ytani01/NixieClock/docs/clock2.jpg

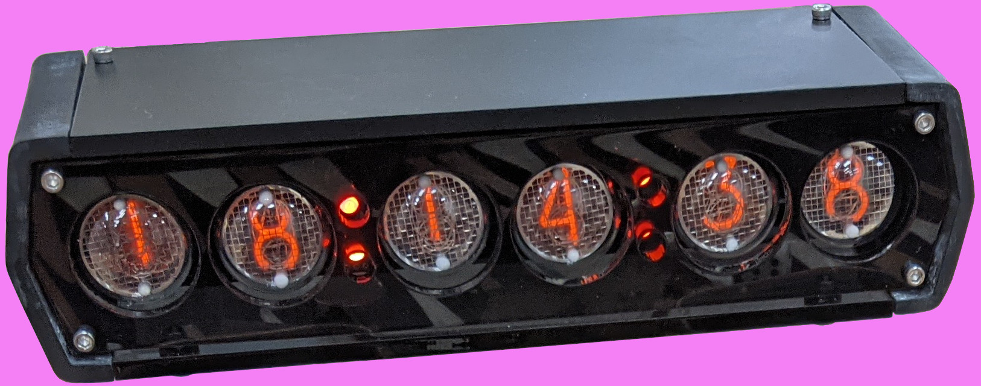
docs/clock2.jpg
