ytani01/NixieClock/Stand/Stand3/Stand3.png

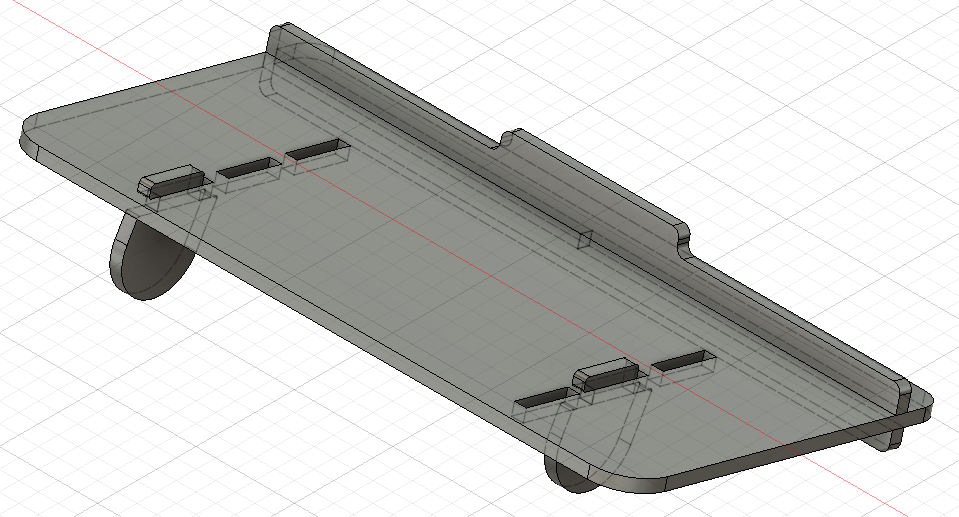
Stand/Stand3/Stand3.png
