ytani01/NixieClock/IN-16/fromTakao/IN-16_Nixie_Clock/drawing/Top_Drawing_0827.dxf

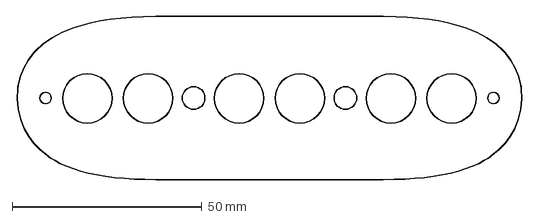
[picture p29: CAD file, 2023-09-14]
IN-16/fromTakao/IN-16_Nixie_Clock/drawing/Top_Drawing_0827.dxf
133.6 x 43.0 mm
