ytani01/NixieClock/IN-16/fromTakao/IN-16_Nixie_Clock/drawing/Spacer_3DPrint_Mid_0824.stl

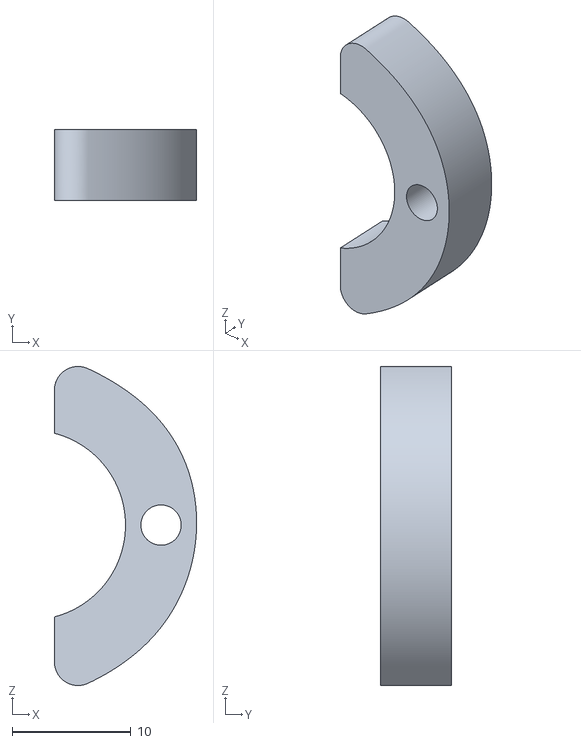
[picture p32: CAD file, 2023-09-14]
IN-16/fromTakao/IN-16_Nixie_Clock/drawing/Spacer_3DPrint_Mid_0824.stl
12.0 x 6.00 x 26.9
