ytani01/NixieClock/IN-16/fromTakao/IN-16_Nixie_Clock/drawing/IN-16_6digit_MCU_Base.dxf

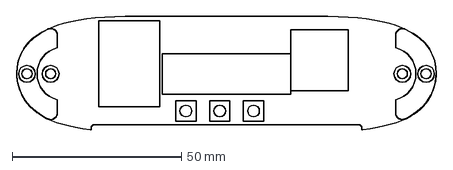
[picture p33: CAD file, 2023-09-14]
IN-16/fromTakao/IN-16_Nixie_Clock/drawing/IN-16_6digit_MCU_Base.dxf
124.5 x 33.5 mm
