ytani01/NixieClock/IN-16/NixieTubeClock/NetMgr.cpp

/**
 * Copyright (c) 2023 Yoichi Tanibayashi
 */
#include "NetMgr.h"

/**
 * Initialize static variables
 */
String NetMgr::myName = "NetMgr";
unsigned int NetMgr::ssidN = 0;
SSIDent NetMgr::ssidEnt[NetMgr::SSID_N_MAX];
WebServer NetMgr::web_svr(WEBSVR_PORT);

/**
 *
 */
NetMgr::NetMgr() {
  this->ap_ip      = IPAddress(this->ap_ip_int[0],
                               this->ap_ip_int[1],
                               this->ap_ip_int[2],
                               this->ap_ip_int[3]);
  this->ap_netmask = IPAddress(this->ap_netmask_int[0],
                               this->ap_netmask_int[1],
                               this->ap_netmask_int[2],
                               this->ap_netmask_int[3]);
} // static WebServer()

/**
 *
 */
mode_t NetMgr::loop() {
  String     myname = "NetMgr::loop";
  ConfWifi conf_data;
  String     ssid, ssid_pw;
  
  this->_loop_count++;

  switch (this->cur_mode) {
  case MODE_NULL:
    break;
    
  case MODE_START:
    log_i("%s> MODE_START", myname);

    conf_data.load();
    ssid = conf_data.ssid;
    ssid_pw = conf_data.ssid_pw;
    log_i("%s> |%s|%s|",
          myname.c_str(), ssid.c_str(), ssid_pw.c_str());

    WiFi.begin(ssid.c_str(), ssid_pw.c_str());
    delay(100);
    this->cur_mode = MODE_TRY_WIFI;
    this->_loop_count = 0;
    break;

  case MODE_TRY_WIFI:
    if (WiFi.status() == WL_CONNECTED) {
      log_i("%s> IPaddr=%s", myname.c_str(), WiFi.localIP().toString().c_str());

      this->net_is_available = true;
      this->cur_mode = MODE_WIFI_ON;
      break;
    }

    if (this->_loop_count > WIFI_TRY_COUNT_MAX) {
      log_w(" WiFi faild");

      this->cur_mode = MODE_AP_INIT;
      break;
    }

    log_i("%s> loop_count=%d", myname.c_str(), this->_loop_count);
    delay(WIFI_TRY_INTERVAL);
    break;

  case MODE_AP_INIT:
    uint8_t mac_int[6];
    char    mac_str[13];
    
    log_i("%s> MODE_AP_INIT", myname.c_str());

    WiFi.disconnect(true);
    WiFi.mode(WIFI_OFF);
    delay(100);

    esp_read_mac(mac_int, ESP_MAC_WIFI_STA);
    sprintf(mac_str, "%02X%02X%02X%02X%02X%02X",
            mac_int[0], mac_int[1], mac_int[2],
            mac_int[3], mac_int[4], mac_int[5]);
    log_i("%s> MacAddr=%s", myname.c_str(), mac_str);

    this->ap_ssid = this->ap_ssid_hdr + String(mac_str);
    log_i("%s> ap_ssid=%s", myname.c_str(), this->ap_ssid.c_str());

    WiFi.mode(WIFI_AP);
    log_i("%s> WiFi.softAP(%s) .. ",
          myname.c_str(), this->ap_ssid.c_str());
    delay(100);

    if ( ! WiFi.softAP(this->ap_ssid.c_str()) ) {
      log_i("%s> .. failed", myname.c_str());
      WiFi.mode(WIFI_OFF);

      this->cur_mode = MODE_WIFI_OFF;
      break;
    }

    log_i("%s> .. start", myname.c_str());
    delay(300);

    WiFi.softAPConfig(this->ap_ip, this->ap_ip, this->ap_netmask);

    this->dns_svr.setErrorReplyCode(DNSReplyCode::NoError);
    this->dns_svr.start(DNS_PORT, "*", this->ap_ip);
    log_i("%s> DNS server[%d] started", myname.c_str(), DNS_PORT);

    NetMgr::async_scan_ssid_start();

    web_svr.enableDelay(false); // Important!!
    web_svr.on("/", NetMgr::handle_top);
    web_svr.on("/select_ssid", NetMgr::handle_select_ssid);
    web_svr.on("/save_ssid", NetMgr::handle_save_ssid);
    web_svr.on("/scan_ssid", NetMgr::handle_do_scan);
    web_svr.on("/confirm_reboot", NetMgr::handle_confirm_reboot);
    web_svr.on("/do_reboot", NetMgr::handle_do_reboot);
    web_svr.onNotFound(NetMgr::handle_top);
    web_svr.begin();
    log_i("%s> Web server[%d] started\n", myname.c_str(), WEBSVR_PORT);

    this->cur_mode = MODE_AP_LOOP;

    break;

  case MODE_AP_LOOP:
    this->dns_svr.processNextRequest();
    web_svr.handleClient();
    break;

  case MODE_WIFI_ON:
    if (WiFi.status() != WL_CONNECTED) {
      this->cur_mode = MODE_WIFI_OFF;
    }
    break;

  case MODE_WIFI_OFF:
    if (WiFi.status() == WL_CONNECTED) {
      this->cur_mode = MODE_WIFI_ON;
    }
    break;

  default:
    log_i("%s> unknown mode ???", myname.c_str());
    delay(1000);
    break;
  } // switch

  return this->cur_mode;
} // NetMgr::loop()

/**
 *
 */
String NetMgr::html_header(String title) {
  String html = "";
  html += "<!DOCTYPE html>";
  html += "<html>";
  html += "<head>";

  html += "<meta name='viewport' content='width=device-width, initial-scale=1'>";
  html += "<meta http-equiv='Pragma' content='no-cache'>";
  html += "<meta http-equiv='Cache-Control' content='no-cache'>";
  html += "<meta http-equiv='Expires' content='0'>";
  html += "<meta http-equiv='Content-type' CONTENT='text/html; charset=utf-8'>";

  html += "<style>";
  html += ".myname {";
  html += "  font-size: xx-large;";
  html += "  text-align: center;";
  html += "  color: #FF0000;";
  html += "  background-color: #444444;";
  html += "}";

  html += ".ssid {";
  html += " font-size: x-large;";
  html += "}";

  html += "a:link, a:visited {";
  html += " background-color: #00AA00;";
  html += " color: white;";
  html += " border: none;";
  html += " text-align: center;";
  html += " text-decoration: none;";
  html += " display: inline-block;";
  html += " padding: 3px 7px;";
  html += "}";

  html += "a:hover, a:active {";
  html += " background-color: #00DD00;";
  html += "}";

  html += "input[type=button], input[type=submit], input[type=reset] {";
  html += " background-color: #0000DD;";
  html += " color: white;";
  html += " text-decoration: none;";
  html += " font-size: large;";
  html += " border: none;";
  html += " padding: 4px 8px;";
  html += "}";
  html += "</style>";

  html += "</head>";
  html += "<body style='background: linear-gradient(to right, #9FF, #5DD);'>";
  html += "<br />";
  html += "<div class='myname'>";
  html += NetMgr::myName;
  html += "</div>";
  html += "<div style='font-size:x-large; color:#00F; background-color: #DDD;'>";
  html += title;
  html += "</div>";
  html += "<hr>";
  return html;
} // NetMgr::handle_header()

String NetMgr::html_footer() {
  String html = "";
  html += "</body>";
  html += "</html>\n";
  return html;
} // NetMgr::html_footer();

void NetMgr::async_scan_ssid_start() {
  log_i("NetMgr::async_scan_ssid_start> ..");
  WiFi.scanNetworks(true);
} // NetMgr::async_scan_ssid_start()

unsigned int NetMgr::async_scan_ssid_wait(SSIDent ssid_ent[]) {
  int16_t ret;

  log_i("NetMgr::async_scan_ssid_wait> ");
  while ( (ret = WiFi.scanComplete()) == WIFI_SCAN_RUNNING ) {
    log_i(".");
    delay(200);
  }
  if ( ret == WIFI_SCAN_FAILED ) {
    return 0;
  }

  if ( ret > NetMgr::SSID_N_MAX ) {
    ret = NetMgr::SSID_N_MAX;
  }

  for (int i=0; i < ret; i++) {
    ssid_ent[i].set(WiFi.SSID(i), WiFi.RSSI(i), WiFi.encryptionType(i));
  } // for()

  return ret;
} // NetMgr::async_scan_ssid_wait()

/**
 *
 */
unsigned int NetMgr::scan_ssid(SSIDent ssid_ent[]) {
  log_i("NetMgr::scan_ssid> scan start ..");

  int ssid_n = WiFi.scanNetworks();

  log_i("NetMgr::scan_ssid> %d SSIDs found\n", ssid_n);

  if (ssid_n <= 0) {
    return 0;
  }

  if ( ssid_n > NetMgr::SSID_N_MAX ) {
    ssid_n = NetMgr::SSID_N_MAX;
  }

  for (int i=0; i < ssid_n; i++) {
    ssid_ent[i].set(WiFi.SSID(i), WiFi.RSSI(i), WiFi.encryptionType(i));
  } // for()

  return ssid_n;
} // NetMgr::ssid_scan()

/**
 *
 */
void NetMgr::handle_top() {
  String   myname = "NetMgr::handle_top";
  ConfWifi conf_data;
  String   ssid, ssid_pw;

  conf_data.load();
  ssid = conf_data.ssid;
  ssid_pw = conf_data.ssid_pw;
  
  log_i("%s> ssid=%s, ssid_pw=%s\n",
        myname.c_str(), ssid.c_str(), ssid_pw.c_str());

  String html = NetMgr::html_header("Current settings");
  html += "<span style='font-size: large;'>";
  html += "SSID: ";
  html += "</span>";
  html += "<span style='font-size: x-large; font-weight: bold'>";
  html += ssid;
  html += "</span>";
  html += "<hr />";
  html += "<a href='/select_ssid'>Change</a>\n";
  html += "or\n";
  html += "<a href='/confirm_reboot'>OK</a>\n";
  html += NetMgr::html_footer();
  web_svr.send(200, "text/html", html);
} // NetMgr::handle_top()

void NetMgr::handle_select_ssid() {
  ConfWifi conf_data;
  String   ssid, ssid_pw;
  

  conf_data.load();
  ssid = conf_data.ssid;
  ssid_pw = conf_data.ssid_pw;
  
  NetMgr::ssidN = NetMgr::async_scan_ssid_wait(NetMgr::ssidEnt);
  log_i("NetMgr::ssidN=%s", String(NetMgr::ssidN));
  if (NetMgr::ssidN == 0) {
    log_i("NetMgr::handle_select_ssid> rescan SSID");
    NetMgr::async_scan_ssid_start();
    NetMgr::ssidN = NetMgr::async_scan_ssid_wait(NetMgr::ssidEnt);
  }

  for (int i=0; i < NetMgr::ssidN; i++) {
    log_i("%s %s %s",
          NetMgr::ssidEnt[i].ssid(),
          String(NetMgr::ssidEnt[i].dbm()),
          NetMgr::ssidEnt[i].encType());
  } // for(i)

  String html = NetMgr::html_header("Please change settings and save");

  html += "<form action='/save_ssid' method='GET'>";
  html += "<div class='ssid'>";
  html += "SSID ";
  html += "<select name='ssid' id='ssid' style='font-size:large;'>";

  for(int i=0; i < NetMgr::ssidN; i++){
    html += "<option value=" + NetMgr::ssidEnt[i].ssid();
    if ( NetMgr::ssidEnt[i].ssid() == ssid ) {
      html += " selected";
    }
    html += ">";
    html += NetMgr::ssidEnt[i].ssid();
    /*
    html += " (";
    html += String(NetMgr::ssidEnt[i].dbm());
    html += ", ";
    html += NetMgr::ssidEnt[i].encType();
    html += ")";
    */
    html += "</option>\n";
  } // for(i)

  html += "<option value="">(clear)</option>\n";
  html += "</select><br />\n";

  html += "Password ";
  html += "<span style='font-size: xx-large'>";
  html += "<input type='password'";
  html += " name='passwd'";
  html += " value='" + ssid_pw + "'";
  html += " />";
  html += "</span>";
  html += "</div>\n";
  html += "<hr />\n";

  html += "<input type='submit' value='Save' />\n";
  html += "<a href='/scan_ssid'>Rescan</a>\n";
  html += "<a href='/'>Cancel</a>\n";

  html += "</form>";
  html += NetMgr::html_footer();

  web_svr.send(200, "text/html", html);
} // NetMgr::handle_select_ssid()

void NetMgr::handle_save_ssid(){
  ConfWifi conf_data;
  String   ssid       = web_svr.arg("ssid");
  String   ssid_pw    = web_svr.arg("passwd");
  
  log_i("save_ssid> |%s|%s|", ssid.c_str(), ssid_pw.c_str());

  conf_data.ssid = ssid;
  conf_data.ssid.trim();
  conf_data.ssid_pw = ssid_pw;
  conf_data.ssid_pw.trim();
  conf_data.print();
 
  conf_data.save();

  // 自動転送
  web_svr.sendHeader("Location", String("/"), true);
  web_svr.send(302, "text/plain", "");
} // NetMgr::handle_save_ssid()

/**
 *
 */
void NetMgr::handle_confirm_reboot() {
  String html = NetMgr::html_header("Reboot confirmation");
  html += "<p>Are you sure to reboot ";
  html += NetMgr::myName;
  html += " ?</p>\n";
  html += "<a href='/do_reboot'>Yes</a>";
  html += " or ";
  html += "<a href='/'>No</a>";
  html += NetMgr::html_footer();
  web_svr.send(200, "text/html", html.c_str());
} // NetMgr::handle_confirm_reboot()

/**
 *
 */
void NetMgr::handle_do_scan() {
  NetMgr::async_scan_ssid_start();

  // 自動転送
  web_svr.sendHeader("Location", String("/select_ssid"), true);
  web_svr.send(302, "text/plain", "");
} // NetMgr::handle_do_rescan()

/**
 *
 */
void NetMgr::handle_do_reboot() {
  String html = NetMgr::html_header("Rebooting ..");
  html += "Please reconnect WiFi ..";
  html += "<hr />";
  html += NetMgr::html_footer();
  web_svr.send(200, "text/html", html.c_str());

  log_i("reboot esp32 ..");
    
  delay(2000);
  ESP.restart();
} // NetMgr::handle_do_reboot()
