ytani01/NixieClock/NixieTubeClock/ModeScore1.cpp

/**
 * (c) 2021 Yoichi Tanibayashi
 */
#include "ModeScore1.h"

/**
 *
 */
ModeScore1::ModeScore1(NixieArray *nxa): ModeBase::ModeBase(nxa, "ModeScore1",
                                                            ModeScore1::TICK_MS) {
  for (int i=0; i < NUM_N; i++) {
    this->_score[i] = 0;
  }
  this->_cur = 0;
  this->_mode = MODE_NONE;
} // ModeScore1::ModeScore1()

/**
 *
 */
void ModeScore1::init(unsigned long start_ms, DateTime& now,
                      int init_val[NIXIE_NUM_N]) {
  Serial.println("ModeScore1::init>");

  init_val[0] = this->_score[0] / 10;
  init_val[1] = this->_score[0] % 10;
  init_val[2] = this->_score[1] / 10;
  init_val[3] = this->_score[1] % 10;
  init_val[4] = this->_score[2] / 10;
  init_val[5] = this->_score[2] % 10;
  
  ModeBase::init(start_ms, now, init_val);

  this->stat = STAT_DONE;
} // ModeScore1::init()

/**
 *
 */
stat_t ModeScore1::loop(unsigned long cur_ms, DateTime& now) {
  char disp_str[NIXIE_NUM_N + 1];
  int  prev_num[NIXIE_NUM_N];

  if ( ModeBase::loop(cur_ms, now) == STAT_SKIP ) {
    return STAT_SKIP;
  }

  /*
  this->get_disp_str(disp_str);

  for (int i=0; i < NIXIE_NUM_N; i++) {
    prev_num[i] = this->_num[i];
    this->_num[i] = int(disp_str[i] - '0');
    NxNumEl(i, prev_num[i]).set_blightness(0);
    NxNumEl(i, this->_num[i]).set_blightness(Nx->blightness);
  } // for(i)
  */

  return STAT_DONE;
} // ModeScore1::loop()

/**
 *
 */
void ModeScore1::get_disp_str(char* disp_str) {
  sprintf(disp_str, "%02d%02d%02d",
          this->_score[0], this->_score[1], this->_score[2]);
  Serial.printf("%s\n", disp_str);
}

/**
 *
 */
void ModeScore1::btn_intr_hdr(unsigned long cur_ms, Button *btn) {
} // ModeScore1::btn_intr_hdr()

/**
 *
 */
void ModeScore1::btn_loop_hdr(unsigned long cur_ms, Button *btn) {
  int n = btn->get_click_count();

  int n1, n2;
  switch ( this->_cur ) {
  case 0: n1 = 0; n2 = 1; break;
  case 1: n1 = 2; n2 = 3; break;
  case 2: n1 = 4; n2 = 5; break;
  } // switch
  
  if ( btn->get_name() == "BTN0" ) {
    if ( btn->is_long_pressed() && ! btn->is_repeated() ) {
      if ( this->_mode == MODE_NONE ) {
        this->_mode = MODE_MODIFY;

        NxNum(n1).blink_start(millis(), BLINK_TICK_MS);
        NxNum(n2).blink_start(millis(), BLINK_TICK_MS);
      } else {
        this->_mode = MODE_NONE;

        NxNum(n1).end_effect();
        NxNum(n2).end_effect();
      }
      return;
    }

    if ( this->_mode != MODE_MODIFY ) {
      return;
    }

    if ( n == 0 ) {
      return;
    }

    NxNum(n1).end_effect();
    NxNum(n2).end_effect();

    this->_cur = (this->_cur + n) % NUM_N;
    Serial.printf("ModeScore1::btn_loop_hdr> cur=%d\n", this->_cur);

    switch ( this->_cur ) {
    case 0: n1 = 0; n2 = 1; break;
    case 1: n1 = 2; n2 = 3; break;
    case 2: n1 = 4; n2 = 5; break;
    } // switch
    
    NxNum(n1).blink_start(millis(), BLINK_TICK_MS);
    NxNum(n2).blink_start(millis(), BLINK_TICK_MS);

    return;
  }

  if ( this->_mode != MODE_MODIFY ) {
    return;
  }

  if ( btn->is_repeated() ) {
    n = 1;
  }
  
  NxNum(n1).end_effect();
  NxNum(n2).end_effect();

  NxNumEl(n1, this->_score[this->_cur] / 10).set_blightness(0);
  NxNumEl(n2, this->_score[this->_cur] % 10).set_blightness(0);

  if ( btn->get_name() == "BTN1" ) {
    this->_score[this->_cur] += n;
    if ( this->_score[this->_cur] > 99 ) {
      this->_score[this->_cur] = 99;
    }
    Serial.printf("ModeScore1::btn_loop_hdr> score[%d]=%d\n",
                  this->_cur, this->_score[this->_cur]);

  }

  if ( btn->get_name() == "BTN2" ) {
    this->_score[this->_cur] -= n;
    if ( this->_score[this->_cur] < 0 ) {
      this->_score[this->_cur] = 0;
    }
    Serial.printf("ModeScore1::btn_loop_hdr> score[%d]=%d\n",
                  this->_cur, this->_score[this->_cur]);
  }

  NxNumEl(n1, this->_score[this->_cur] / 10).set_blightness(Nx->blightness);
  NxNumEl(n2, this->_score[this->_cur] % 10).set_blightness(Nx->blightness);

  NxNum(n1).blink_start(millis(), BLINK_TICK_MS);
  NxNum(n2).blink_start(millis(), BLINK_TICK_MS);
  
} // ModeScore1::btn_loop_hdr()
