ytani01/NixieClock/test/neopixel-FastLED/neopixel-FastLED.ino

#include <FastLED.h>

const uint8_t  PIN_ONBOARD_LED = 5;

const uint8_t  PIN_PIXEL  = 16;
const uint16_t PIXELS_N   = 6 + 7;
const uint8_t  BLIGHTNESS = 30;

const int      LOOP_DELAY = 1000;

CRGB pixels[PIXELS_N];

int Col[][3] =
{
  {BLIGHTNESS,0,0},
  {0,BLIGHTNESS,0},
  {0,0,BLIGHTNESS},
  {BLIGHTNESS,BLIGHTNESS,0},
  {0,BLIGHTNESS,BLIGHTNESS},
  {BLIGHTNESS,0,BLIGHTNESS},
  {BLIGHTNESS,BLIGHTNESS,BLIGHTNESS}
};

const int COL_N = sizeof(Col) / sizeof(Col[0]);
int Col_i = 0;

void setup() {
  Serial.begin(115200);

  Col_i = 0;

  pinMode(PIN_ONBOARD_LED, OUTPUT);
  digitalWrite(PIN_ONBOARD_LED, LOW);

  FastLED.addLeds<WS2812B, PIN_PIXEL, GRB>(pixels, PIXELS_N);
  FastLED.setBrightness(BLIGHTNESS);
}

void loop() {
  for (int i=0; i < PIXELS_N; i++) {
    int cl = (Col_i + i) % COL_N;
    Serial.printf("loop> cl=%d\n", cl);

    pixels[i] = CRGB(Col[cl][0], Col[cl][1], Col[cl][2]);
  }
  FastLED.show();

  Col_i = (Col_i + 1) % COL_N;
  delay(LOOP_DELAY);
}
